RavinduLK/CocoExpert-Level1-HardwareProject/Documents/Final Schematic Diagram.png

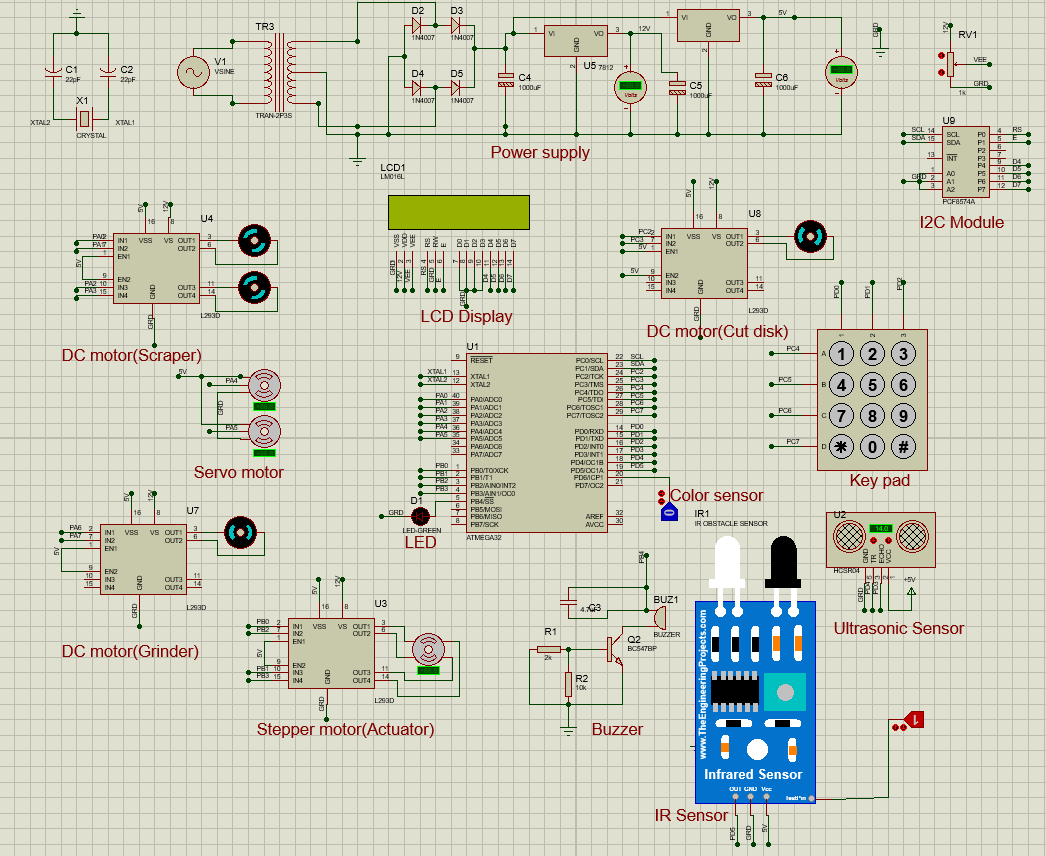
Documents/Final Schematic Diagram.png
