RavinduLK/CocoExpert-Level1-HardwareProject/Documents/Sample Image.png

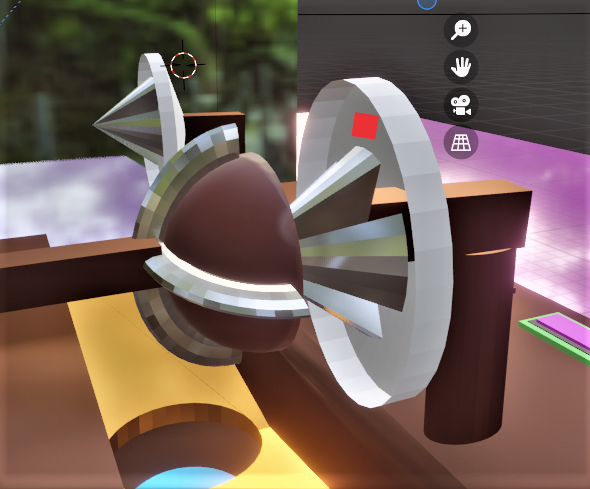
Documents/Sample Image.png
