RavinduLK/CocoExpert-Level1-HardwareProject/Simulations/PCB Files/204018x-PCB Files/204018x-PCB Files/power_supply/power_supply3D.png

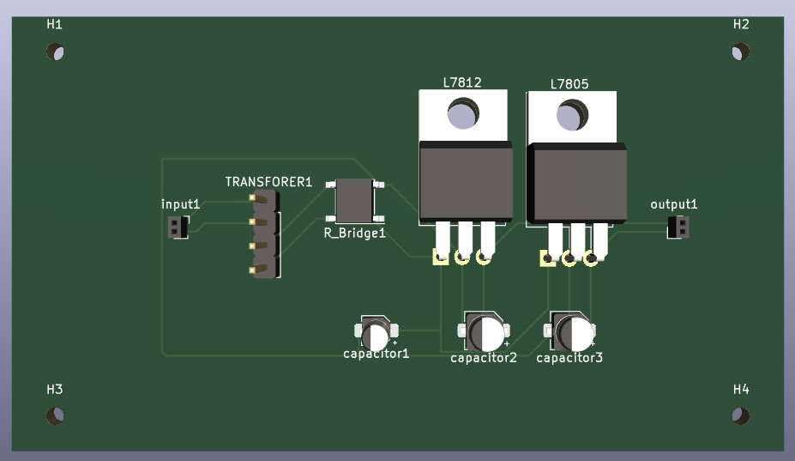
Simulations/PCB Files/204018x-PCB Files/204018x-PCB Files/power_supply/power_supply3D.png
