RavinduLK/CocoExpert-Level1-HardwareProject/Simulations/PCB Files/204018x-PCB Files/204018x-PCB Files/power_supply/powerSupply_pcb.png

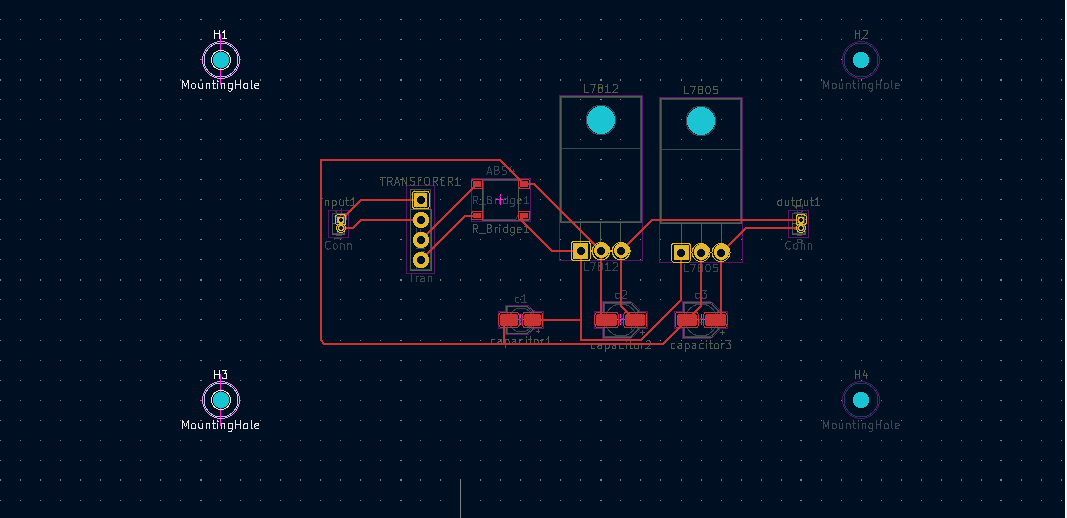
Simulations/PCB Files/204018x-PCB Files/204018x-PCB Files/power_supply/powerSupply_pcb.png
