RavinduLK/CocoExpert-Level1-HardwareProject/Simulations/PCB Files/204018x-PCB Files/204018x-PCB Files/stepper/stepper3D.png

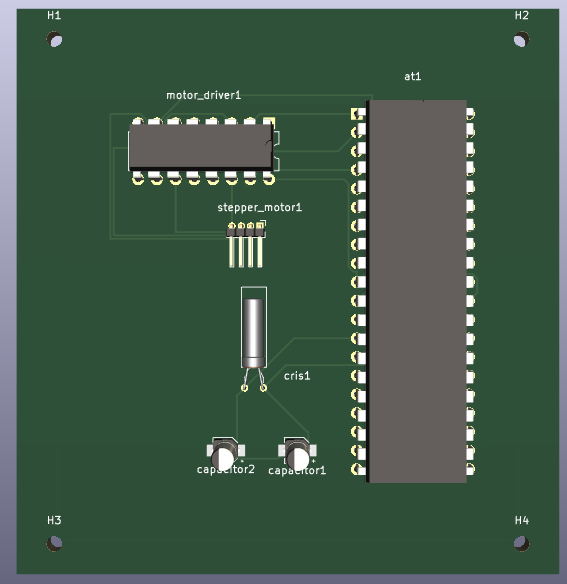
Simulations/PCB Files/204018x-PCB Files/204018x-PCB Files/stepper/stepper3D.png
