RavinduLK/CocoExpert-Level1-HardwareProject/Simulations/PCB Files/204096G-PCBs/204096G-PCBs'/PCB & Schematic Files-Buzzer/Buzzer-3D View(PCB).png

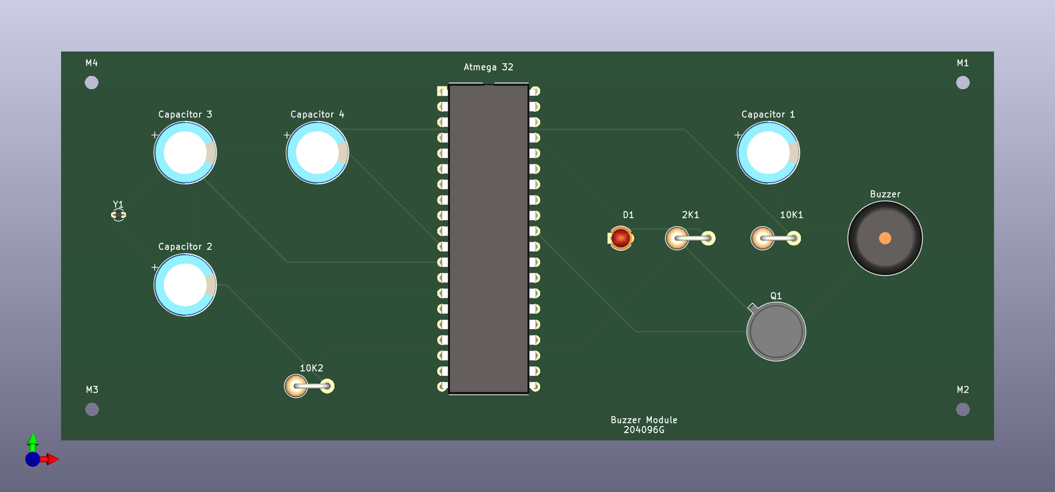
Simulations/PCB Files/204096G-PCBs/204096G-PCBs'/PCB & Schematic Files-Buzzer/Buzzer-3D View(PCB).png
