RavinduLK/CocoExpert-Level1-HardwareProject/Simulations/PCB Files/204096G-PCBs/204096G-PCBs'/PCB & Schematic Files-Buzzer/Schematic Diagram-Screenshot.png

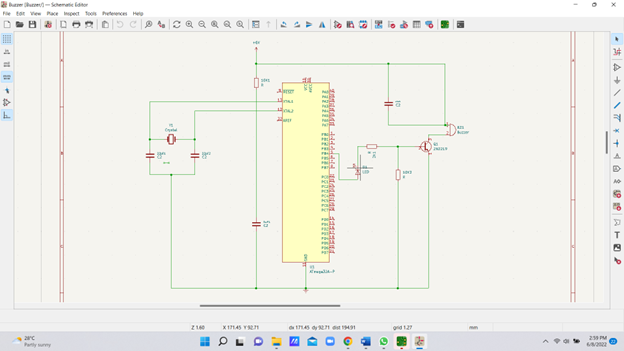
Simulations/PCB Files/204096G-PCBs/204096G-PCBs'/PCB & Schematic Files-Buzzer/Schematic Diagram-Screenshot.png
