RavinduLK/CocoExpert-Level1-HardwareProject/Simulations/PCB Files/204096G-PCBs/204096G-PCBs'/PCB & Schematic Files-Servo/3D View-PCB Design.png

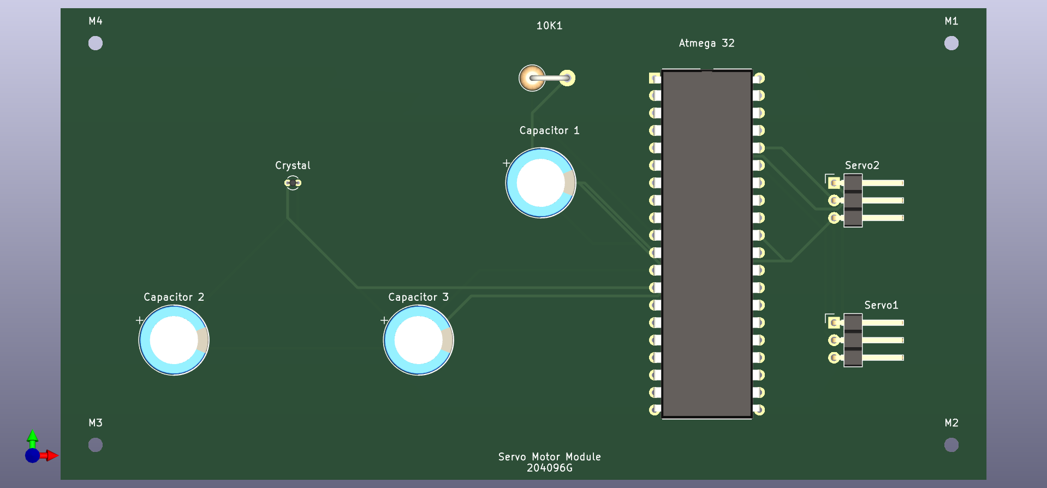
Simulations/PCB Files/204096G-PCBs/204096G-PCBs'/PCB & Schematic Files-Servo/3D View-PCB Design.png
