RavinduLK/CocoExpert-Level1-HardwareProject/Simulations/PCB Files/204108A-PCB Files/204108A-PCB Files/colour_sensor/colour_sensor_schematic_ss.PNG

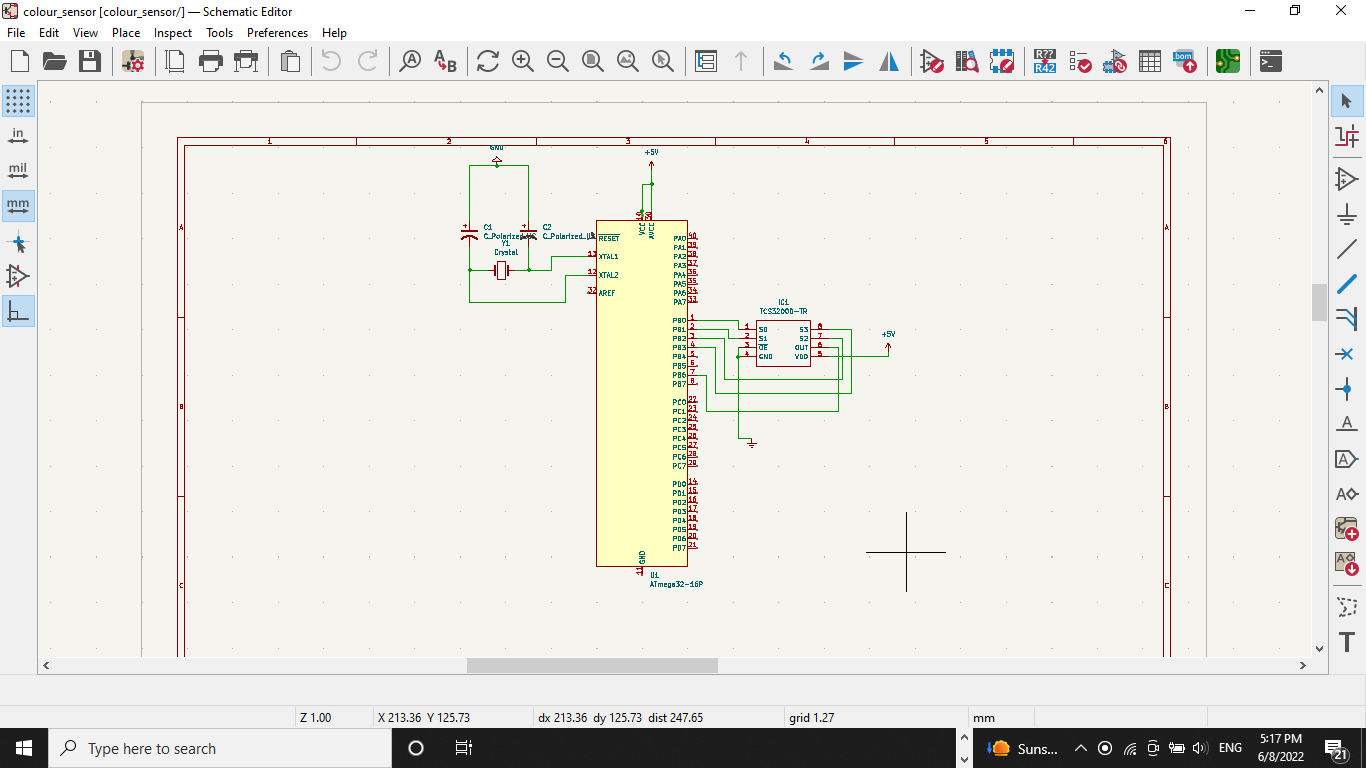
Simulations/PCB Files/204108A-PCB Files/204108A-PCB Files/colour_sensor/colour_sensor_schematic_ss.PNG
