RavinduLK/CocoExpert-Level1-HardwareProject/Simulations/PCB Files/204108A-PCB Files/204108A-PCB Files/cut_disk_OR_blender/cut_disk_OR_blender_3d_ss.PNG

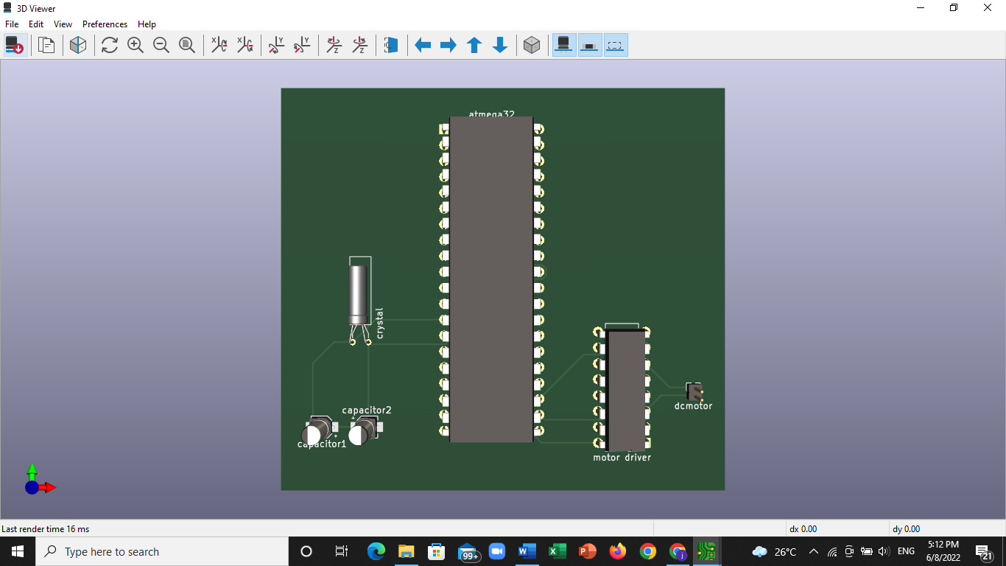
Simulations/PCB Files/204108A-PCB Files/204108A-PCB Files/cut_disk_OR_blender/cut_disk_OR_blender_3d_ss.PNG
