RavinduLK/CocoExpert-Level1-HardwareProject/Simulations/PCB Files/204108A-PCB Files/204108A-PCB Files/scrapper/scrapper_3d_ss.PNG

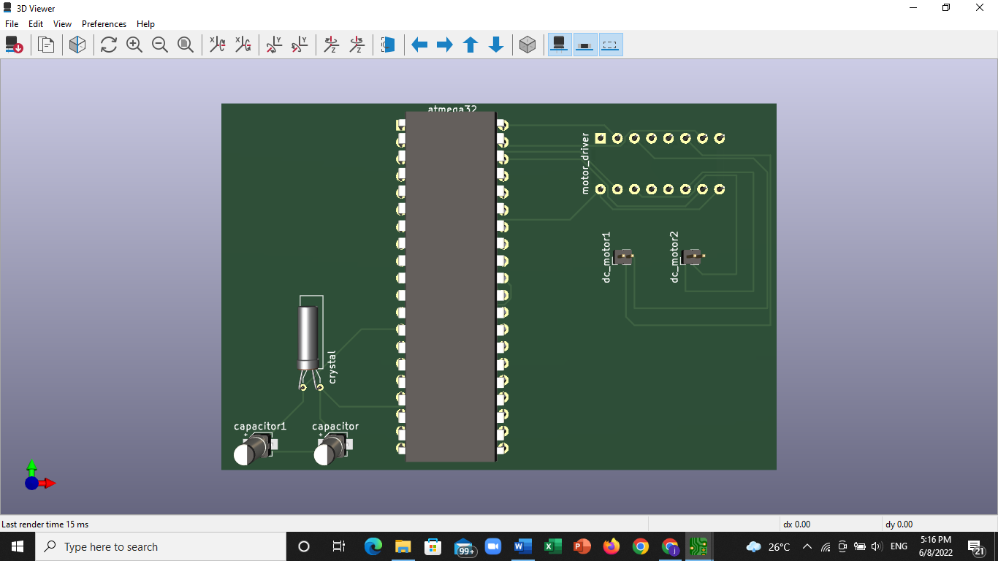
Simulations/PCB Files/204108A-PCB Files/204108A-PCB Files/scrapper/scrapper_3d_ss.PNG
