RavinduLK/CocoExpert-Level1-HardwareProject/Simulations/PCB Files/204114M-PCB Files/204114M-PCB Files/Ir new/IR sensor schematic.png

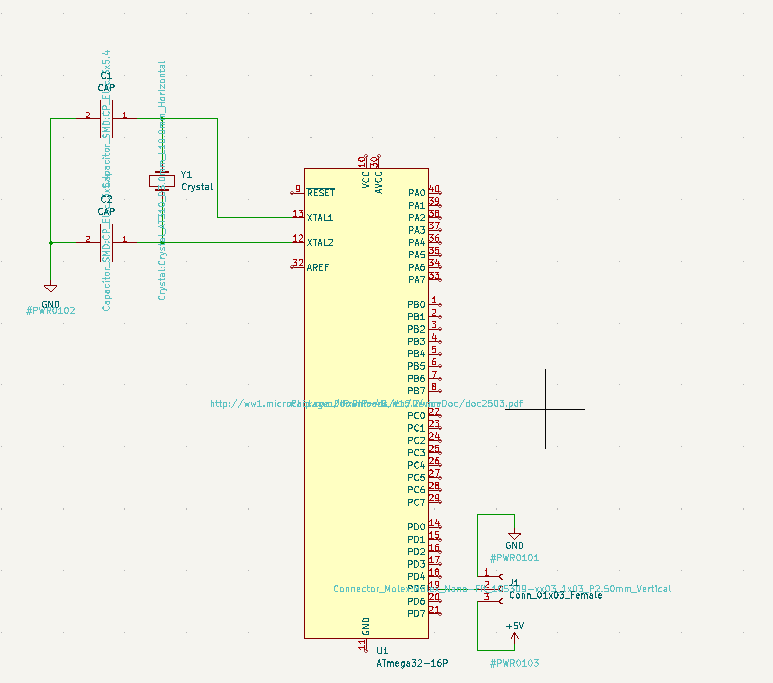
Simulations/PCB Files/204114M-PCB Files/204114M-PCB Files/Ir new/IR sensor schematic.png
