RavinduLK/CocoExpert-Level1-HardwareProject/Simulations/PCB Files/204114M-PCB Files/204114M-PCB Files/keypad/Keypad 3D.png

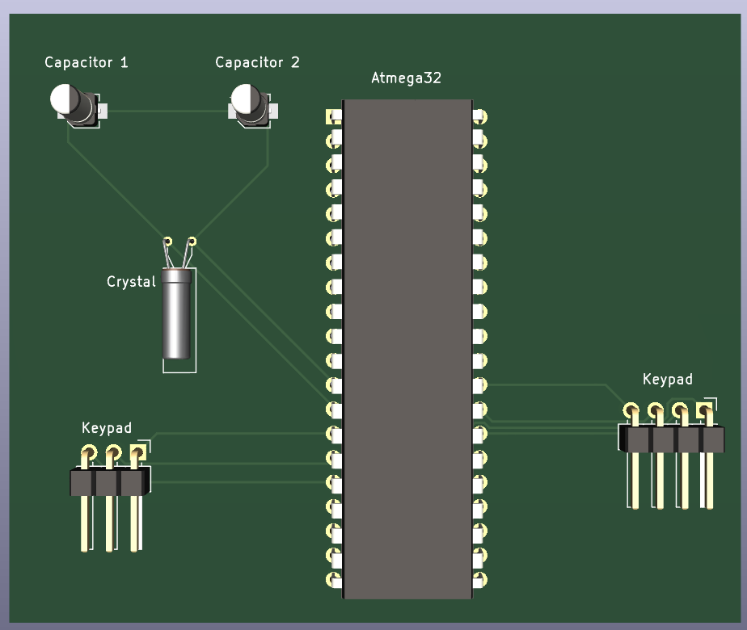
Simulations/PCB Files/204114M-PCB Files/204114M-PCB Files/keypad/Keypad 3D.png
