RavinduLK/CocoExpert-Level1-HardwareProject/Simulations/PCB Files/204114M-PCB Files/204114M-PCB Files/keypad/Keypad PCB.png

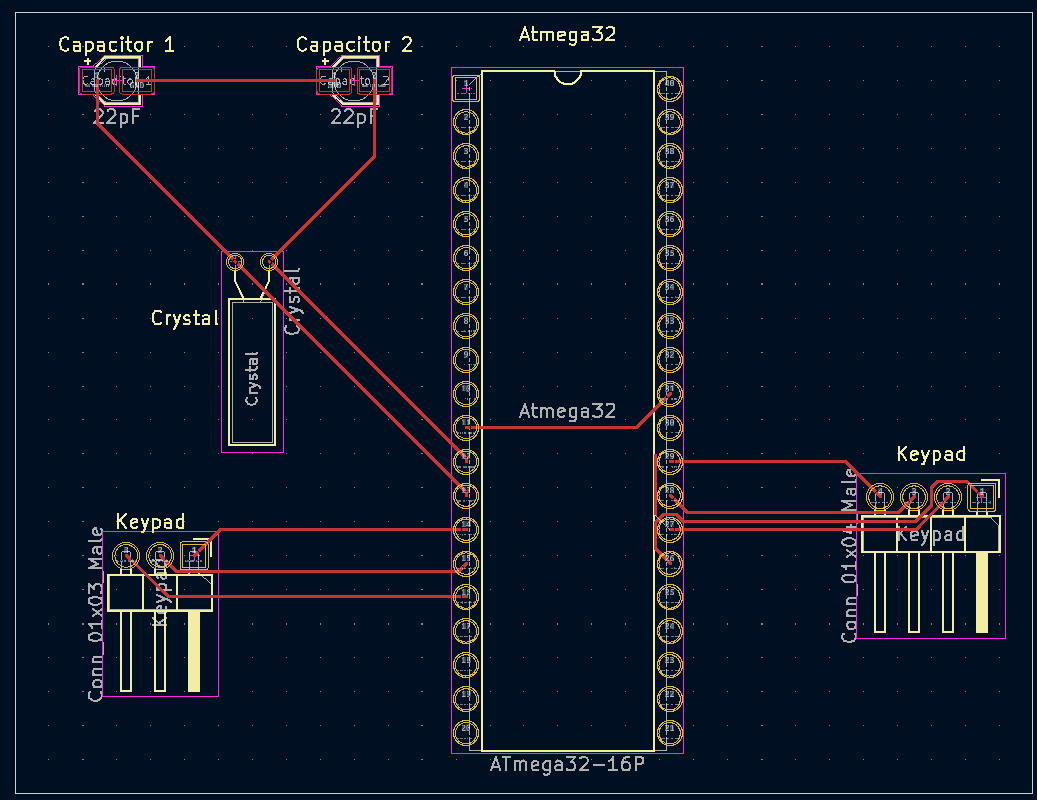
Simulations/PCB Files/204114M-PCB Files/204114M-PCB Files/keypad/Keypad PCB.png
