RavinduLK/CocoExpert-Level1-HardwareProject/Simulations/PCB Files/204146L-PCB Files/204146L-PCB Files/LCD-display(204146L)/Lcd schematic screenshot.png

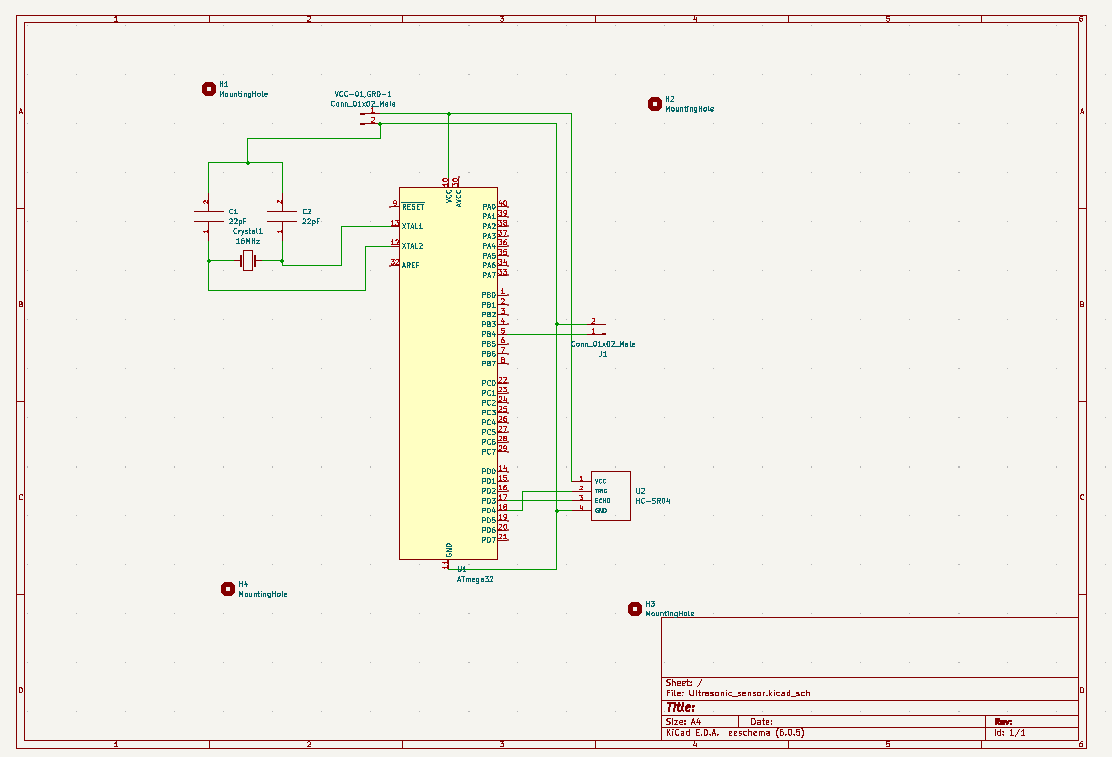
Simulations/PCB Files/204146L-PCB Files/204146L-PCB Files/LCD-display(204146L)/Lcd schematic screenshot.png
