RavinduLK/CocoExpert-Level1-HardwareProject/Simulations/PCB Files/204146L-PCB Files/204146L-PCB Files/LCD-display(204146L)/LCD_Display 3D view.png

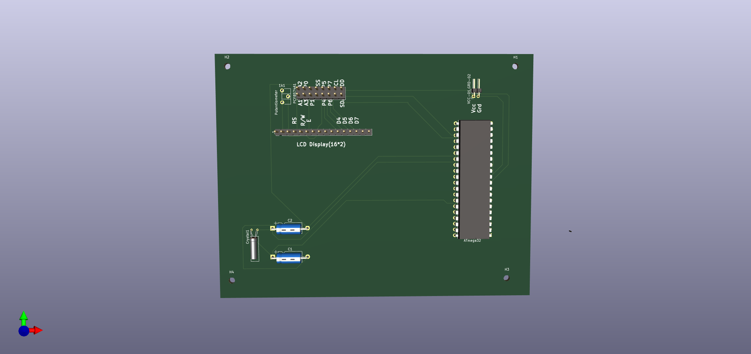
Simulations/PCB Files/204146L-PCB Files/204146L-PCB Files/LCD-display(204146L)/LCD_Display 3D view.png
