RavinduLK/CocoExpert-Level1-HardwareProject/Simulations/PCB Files/204146L-PCB Files/204146L-PCB Files/LCD-display(204146L)/LCD_Display pcb screenshot.PNG

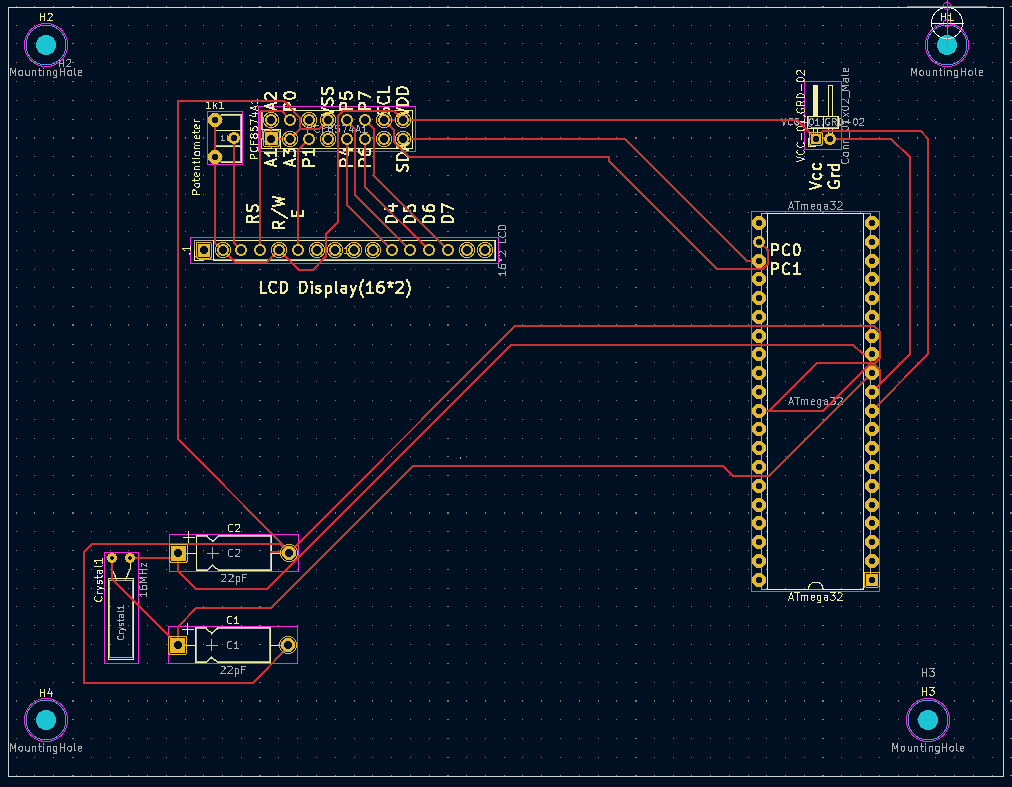
Simulations/PCB Files/204146L-PCB Files/204146L-PCB Files/LCD-display(204146L)/LCD_Display pcb screenshot.PNG
