RavinduLK/CocoExpert-Level1-HardwareProject/Simulations/PCB Files/204146L-PCB Files/204146L-PCB Files/Ultarsonic_Sensor(204146L)/Ultrasonic pcb screenshot.PNG

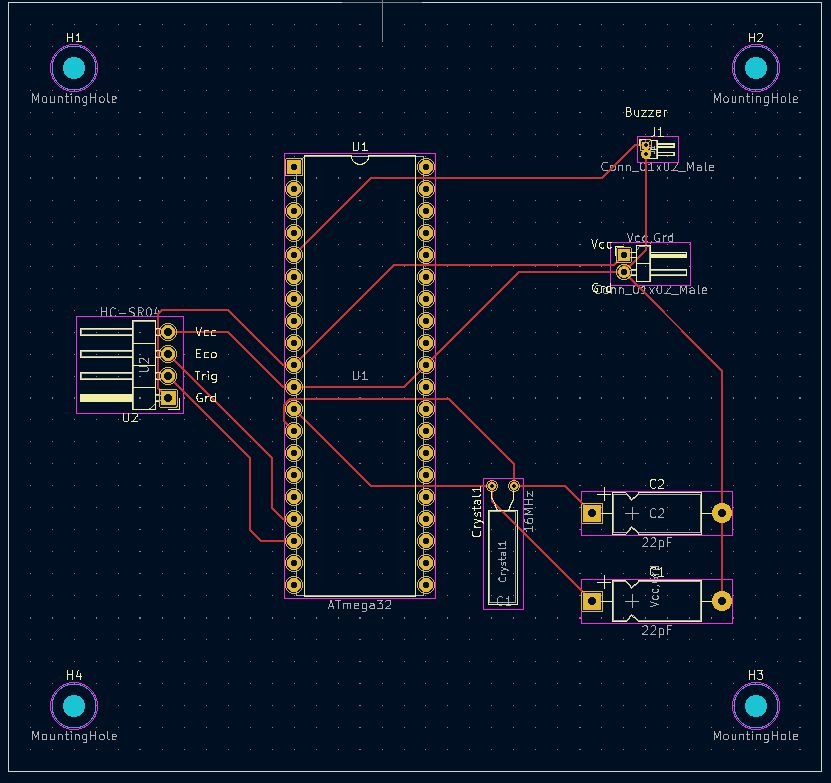
Simulations/PCB Files/204146L-PCB Files/204146L-PCB Files/Ultarsonic_Sensor(204146L)/Ultrasonic pcb screenshot.PNG
