RavinduLK/CocoExpert-Level1-HardwareProject/Simulations/PCB Files/Finale full PCB(Group15)/Finale full PCB(Group15)/Finale pcb schreenshot.PNG

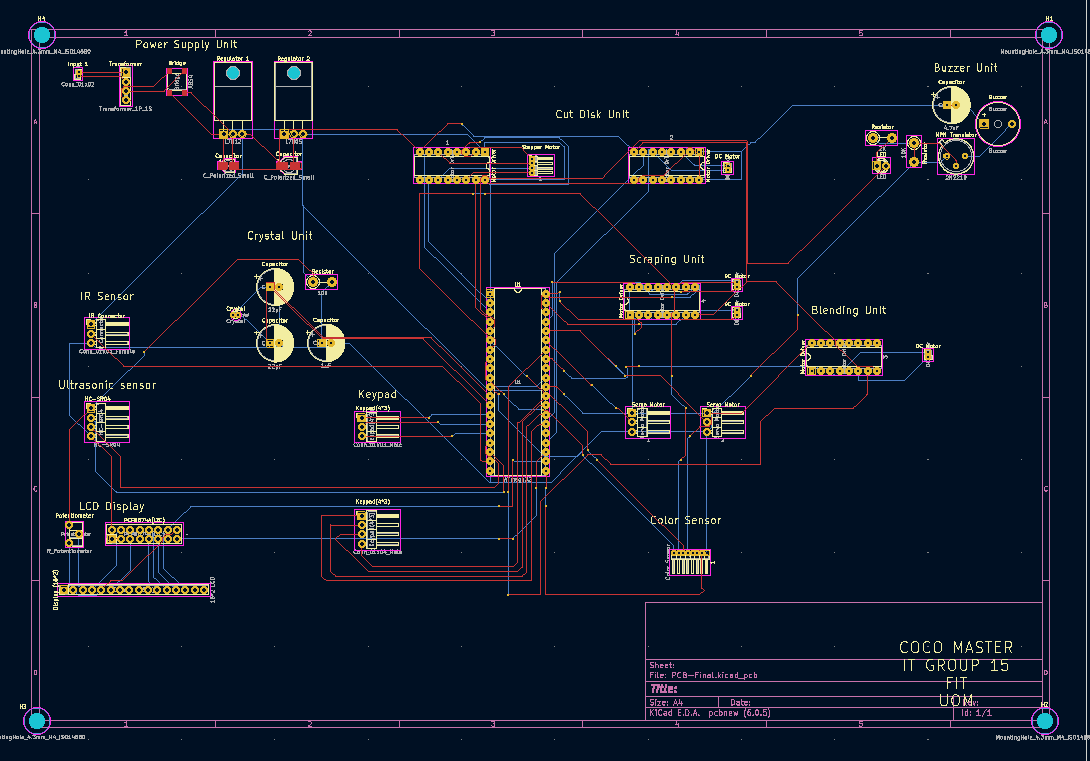
Simulations/PCB Files/Finale full PCB(Group15)/Finale full PCB(Group15)/Finale pcb schreenshot.PNG
