RavinduLK/CocoExpert-Level1-HardwareProject/Simulations/PCB Files/Finale full PCB(Group15)/Finale full PCB(Group15)/Finale shematic screenshot.PNG

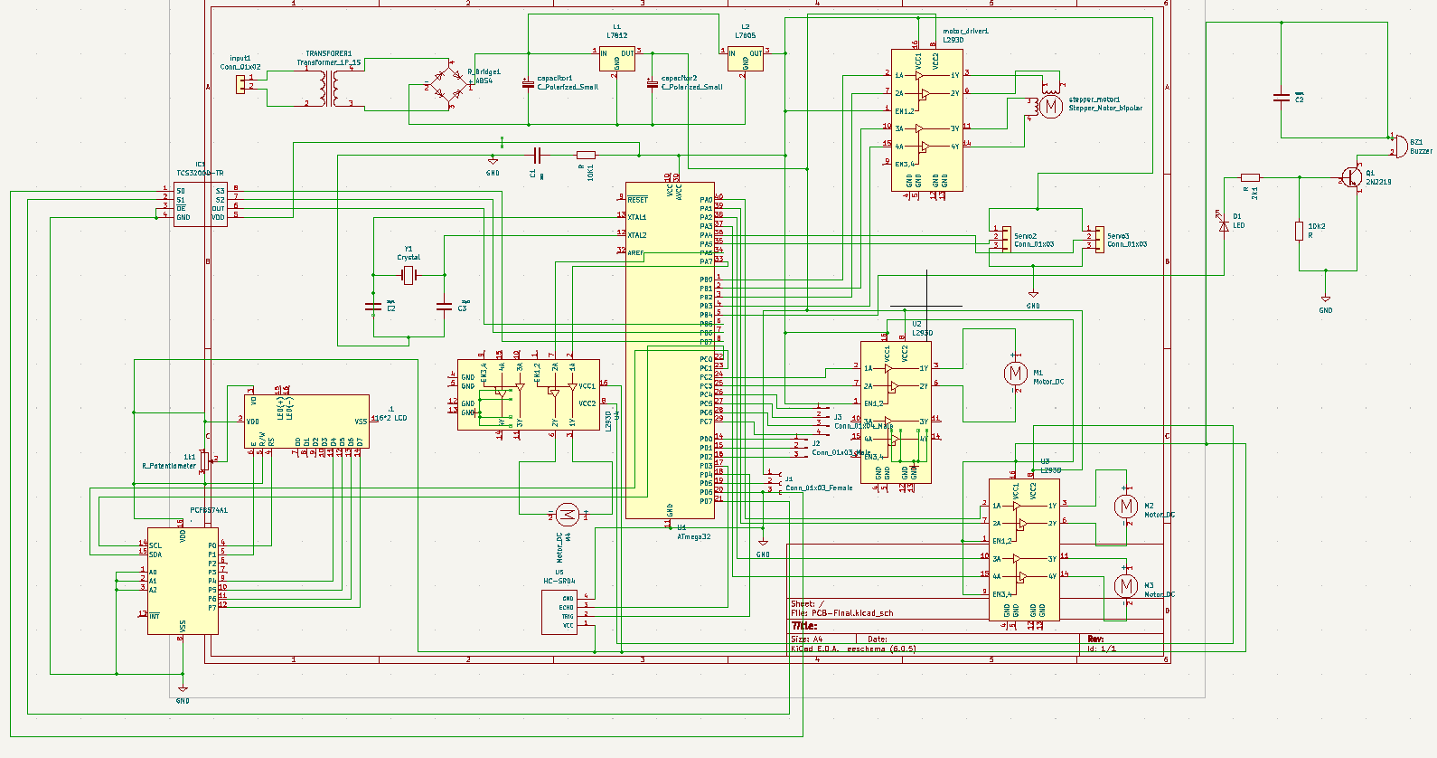
Simulations/PCB Files/Finale full PCB(Group15)/Finale full PCB(Group15)/Finale shematic screenshot.PNG
