RavinduLK/CocoExpert-Level1-HardwareProject/Simulations/PCB Files/Finale full PCB(Group15)/Finale full PCB(Group15)/PCB-Final 3D View.png

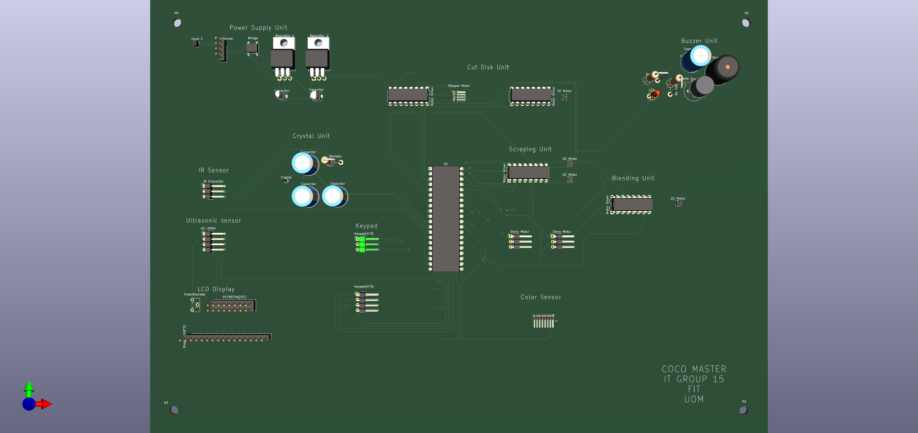
Simulations/PCB Files/Finale full PCB(Group15)/Finale full PCB(Group15)/PCB-Final 3D View.png
