RavinduLK/CocoExpert-Level1-HardwareProject/Simulations/Testing and Implementation Images/Screenshot (653).png

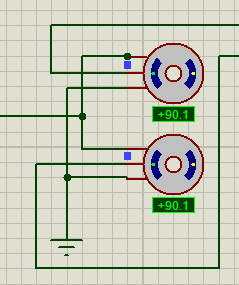
Simulations/Testing and Implementation Images/Screenshot (653).png
