RavinduLK/CocoExpert-Level1-HardwareProject/Simulations/Testing and Implementation Images/Screenshot (655).png

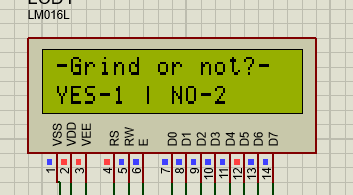
Simulations/Testing and Implementation Images/Screenshot (655).png
