RavinduLK/CocoExpert-Level1-HardwareProject/Simulations/Testing and Implementation Images/Screenshot (657).png

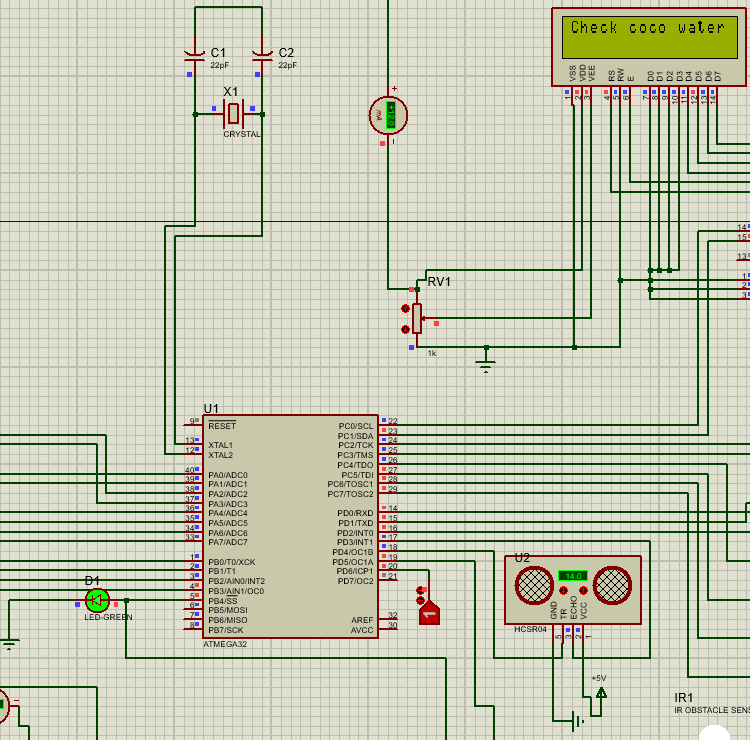
Simulations/Testing and Implementation Images/Screenshot (657).png
