RavinduLK/CocoExpert-Level1-HardwareProject/Simulations/Testing and Implementation Images/Screenshot (658).png

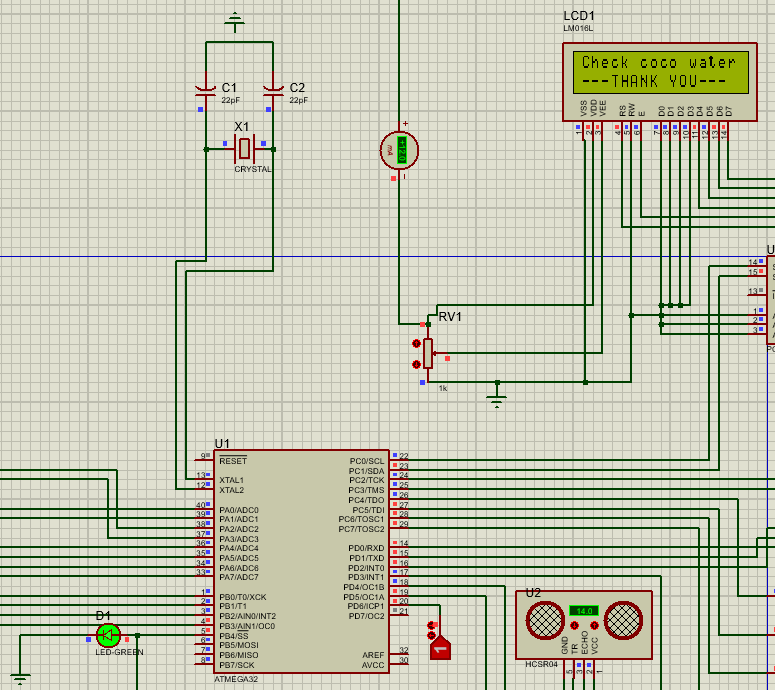
Simulations/Testing and Implementation Images/Screenshot (658).png
