RavinduLK/CocoExpert-Level1-HardwareProject/Simulations/Testing and Implementation Images/Screenshot (659).png

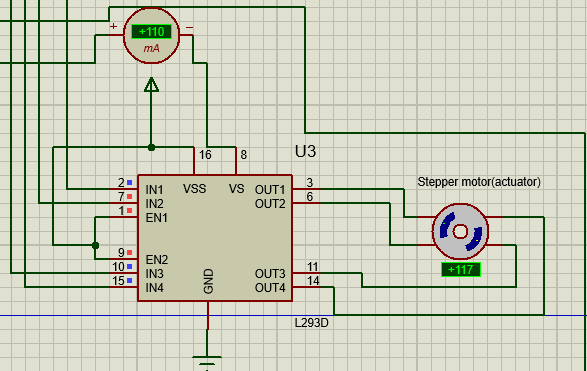
Simulations/Testing and Implementation Images/Screenshot (659).png
