RavinduLK/CocoExpert-Level1-HardwareProject/My Parts/PCB Files/PCB & Schematic Files-Servo/PCB & Schematic Files/Servo.kicad_pcb

## KiCad design My Parts/PCB Files/PCB & Schematic Files-Servo/PCB & Schematic Files/Servo.kicad_pcb (2023-06-24)

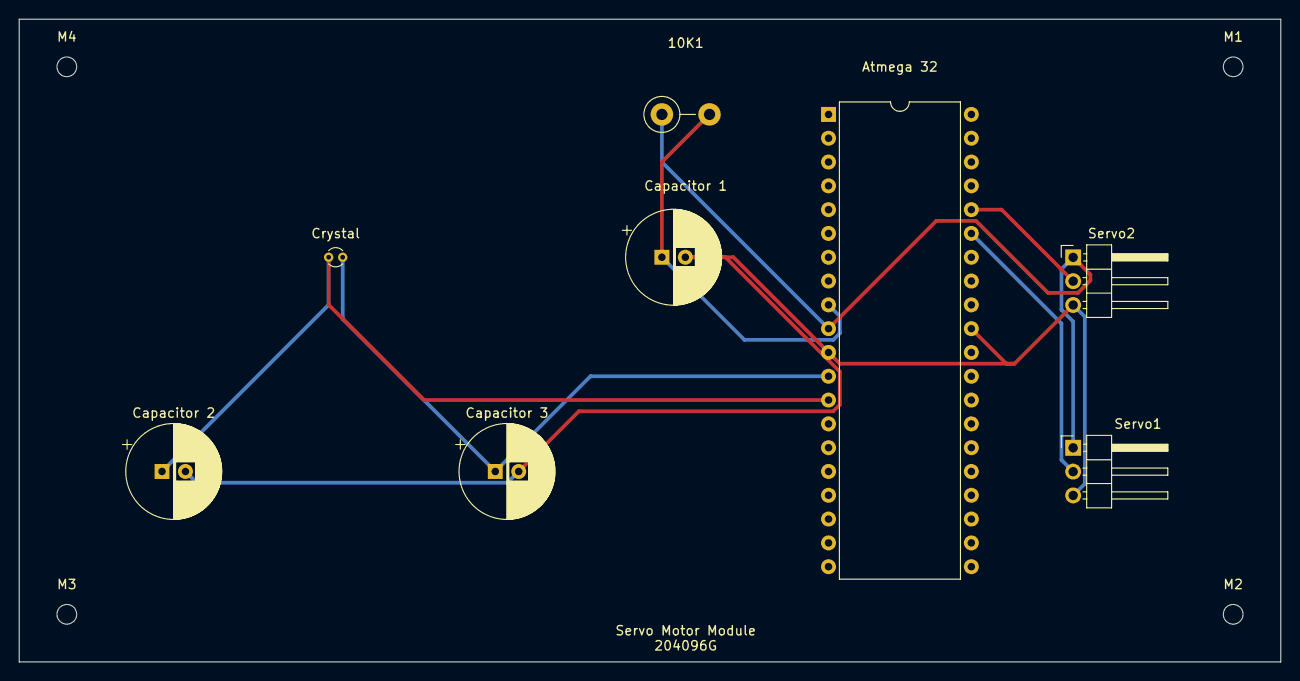
[picture p131: board Servo.kicad_pcb from above]

Board: 2 copper layers, 134.6 x 68.6 mm, 12 parts (0 on the bottom side), 7 nets.

Parts:
10K1: Resistor; R_Axial_DIN0411_L9.9mm_D3.6mm_P5.08mm_Vertical
Atmega 32: ATmega32A-P; DIP-40_W15.24mm
Capacitor 1: 1uF; CP_Radial_D10.0mm_P2.50mm
Capacitor 2, Capacitor 3: 22pF; CP_Radial_D10.0mm_P2.50mm
Crystal: Y1; Crystal_DS10_D1.0mm_L4.3mm_Vertical
M1, M2, M3, M4: MountingHole_2.1mm
Servo1, Servo2: Conn_01x03; PinHeader_1x03_P2.54mm_Horizontal

Connections:
+5V: 10K1.1, Atmega 32.10 (VCC), Servo1.1, Servo2.1
Earth: Atmega 32.11 (GND), Atmega 32.31 (GND), Capacitor 1.2, Capacitor 2.2, Capacitor 3.2, Servo1.3, Servo2.3
unnamed: 10K1.2, Atmega 32.9 (~RESET), Capacitor 1.1
unnamed: Atmega 32.13 (XTAL1), Capacitor 2.1, Crystal.1
unnamed: Atmega 32.12 (XTAL2), Capacitor 3.1, Crystal.2
unnamed: Atmega 32.35 (PA5), Servo1.2
unnamed: Atmega 32.36 (PA4), Servo2.2
